eshazen/blinky-avr-smt/Case2/blinky_3D_front.jpg

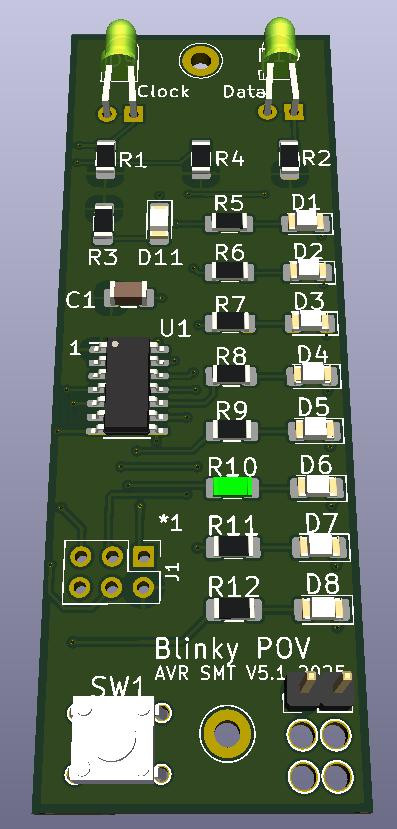
Case2/blinky_3D_front.jpg
