eshazen/blinky-avr-smt/Hardware/BlinkyPov/BlinkyPovAVR4/tute1.kicad_sch

## KiCad design Hardware/BlinkyPov/BlinkyPovAVR4/tute1.kicad_sch (2025-12-15)

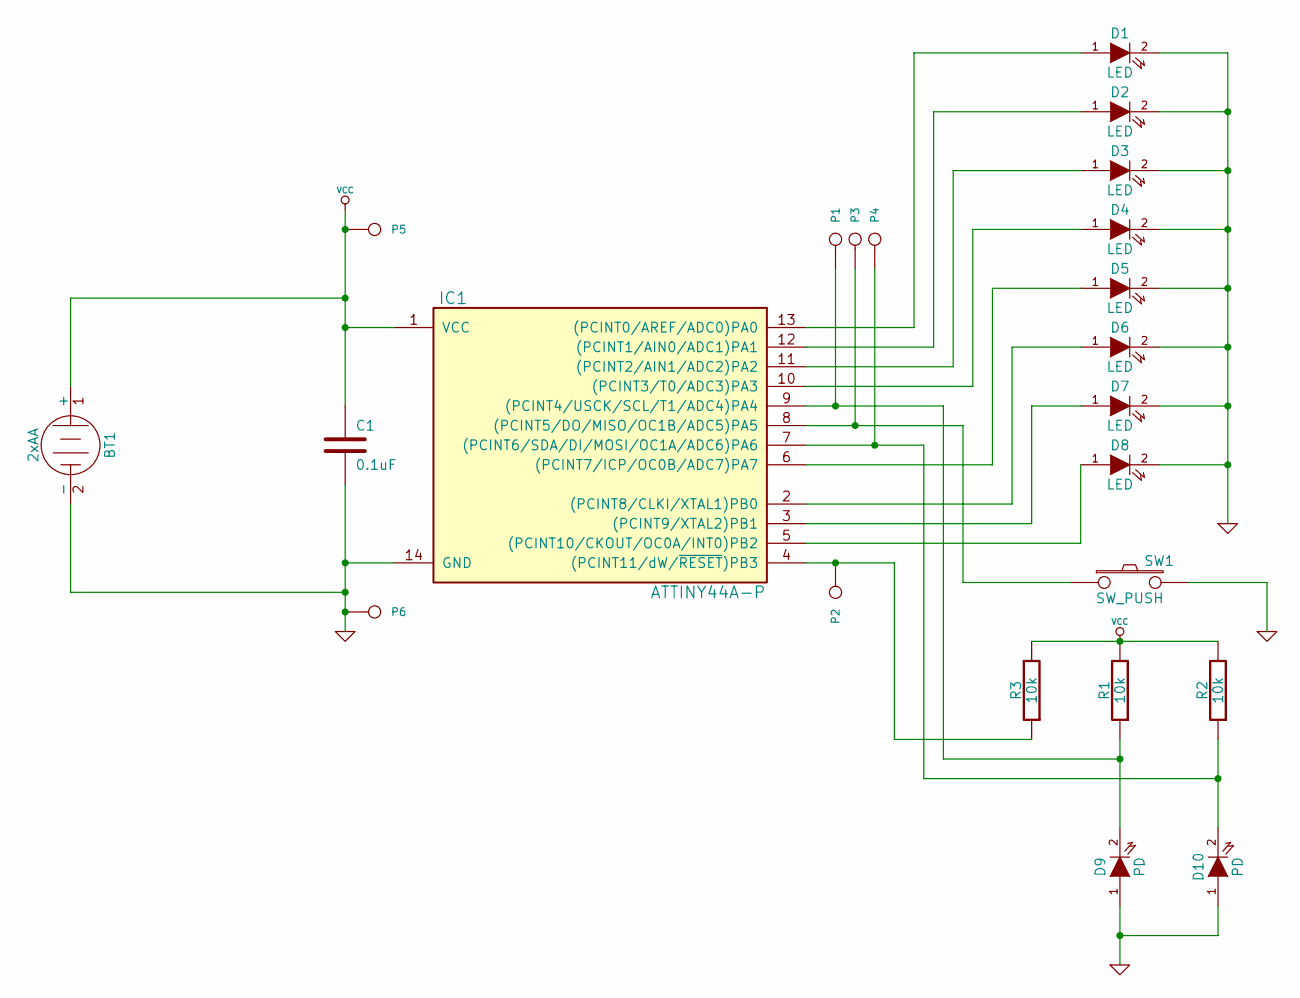
[picture p61: schematic tute1.kicad_sch]

Parts:
BT1: 2xAA
C1: 0.1uF
D1, D2, D3, D4, D5, D6, D7, D8: LED
D9, D10: PD
IC1: ATTINY44A-P; DIP14
P1, P2, P3, P4, P5, P6: CONN_1
R1, R2, R3: 10k
SW1: SW_PUSH

Connections:
GND: BT1.2 (-), C1.2, D1.2 (K), D2.2 (K), D3.2 (K), D4.2 (K), D5.2 (K), D6.2 (K), D7.2 (K), D8.2 (K), D9.1 (A), D10.1 (A), IC1.14 (GND), P6.1, SW1.2
unnamed: D1.1 (A), IC1.13 ((PCINT0/AREF/ADC0)PA0)
unnamed: D2.1 (A), IC1.12 ((PCINT1/AIN0/ADC1)PA1)
unnamed: D3.1 (A), IC1.11 ((PCINT2/AIN1/ADC2)PA2)
unnamed: D4.1 (A), IC1.10 ((PCINT3/T0/ADC3)PA3)
unnamed: D5.1 (A), IC1.6 ((PCINT7/ICP/OC0B/ADC7)PA7)
unnamed: D6.1 (A), IC1.2 ((PCINT8/CLKI/XTAL1)PB0)
unnamed: D7.1 (A), IC1.3 ((PCINT9/XTAL2)PB1)
unnamed: D8.1 (A), IC1.5 ((PCINT10/CKOUT/OC0A/INT0)PB2)
unnamed: D9.2 (K), IC1.9 ((PCINT4/USCK/SCL/T1/ADC4)PA4), P1.1, R1.1
unnamed: D10.2 (K), IC1.7 ((PCINT6/SDA/DI/MOSI/OC1A/ADC6)PA6), P4.1, R2.1
unnamed: IC1.4 ((PCINT11/dW/~RESET)PB3), P2.1, R3.1
unnamed: IC1.8 ((PCINT5/DO/MISO/OC1B/ADC5)PA5), P3.1, SW1.1
VCC: BT1.1 (+), C1.1, IC1.1 (VCC), P5.1, R1.2, R2.2, R3.2
